inceptionev/PlasmaTransformer/3D Print and CNC/ConformalCoatingJig.stl

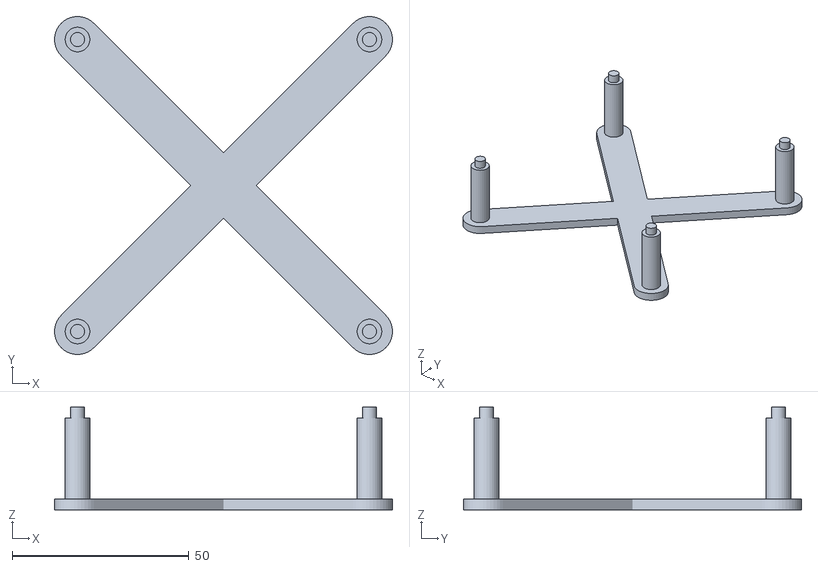
[picture p19: CAD file, 2025-08-11]
3D Print and CNC/ConformalCoatingJig.stl
95.5 x 95.5 x 29.0
