inceptionev/PlasmaTransformer/3D Print and CNC/15cmPasteMaskTemplate.stl

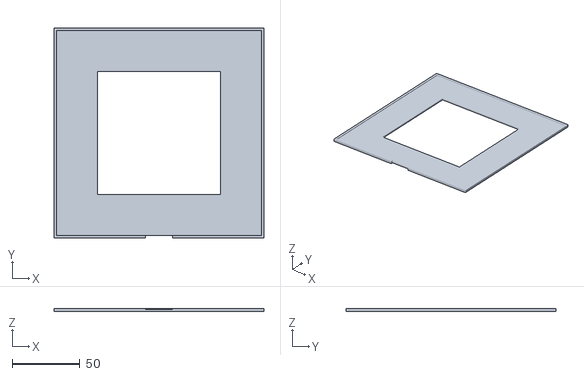
[picture p20: CAD file, 2025-07-31]
3D Print and CNC/15cmPasteMaskTemplate.stl
154.6 x 154.6 x 2.50
