inceptionev/PlasmaTransformer/3D Print and CNC/heatsink-dual-CNC.dxf

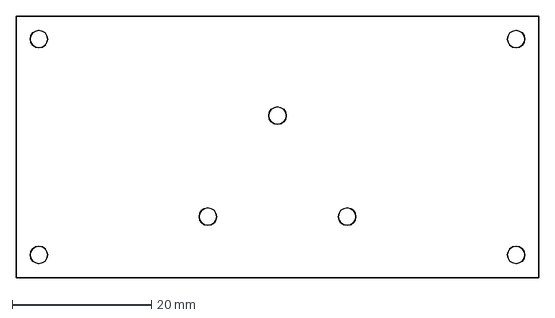
[picture p21: CAD file, 2025-06-07]
3D Print and CNC/heatsink-dual-CNC.dxf
75.0 x 37.5 mm
