inceptionev/PlasmaTransformer/3D Print and CNC/FanShroud-20cm.stl

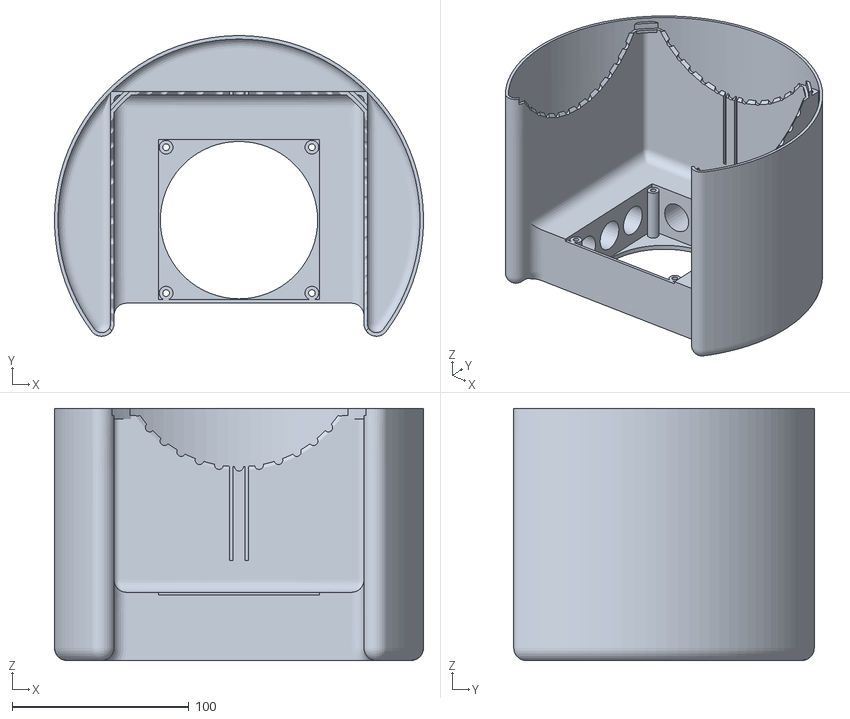
[picture p22: CAD file, 2025-05-27]
3D Print and CNC/FanShroud-20cm.stl
208.8 x 170.1 x 142.6
