inceptionev/PlasmaTransformer/3D Print and CNC/FanShroud-Foot.stl

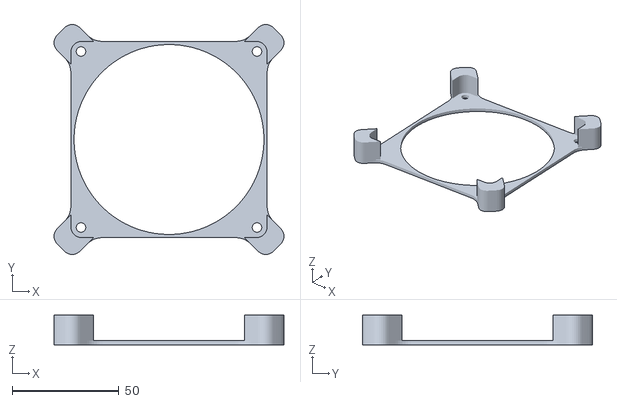
[picture p23: CAD file, 2025-05-27]
3D Print and CNC/FanShroud-Foot.stl
107.8 x 107.8 x 14.0
