inceptionev/PlasmaTransformer/3D Print and CNC/FanShroud.stl

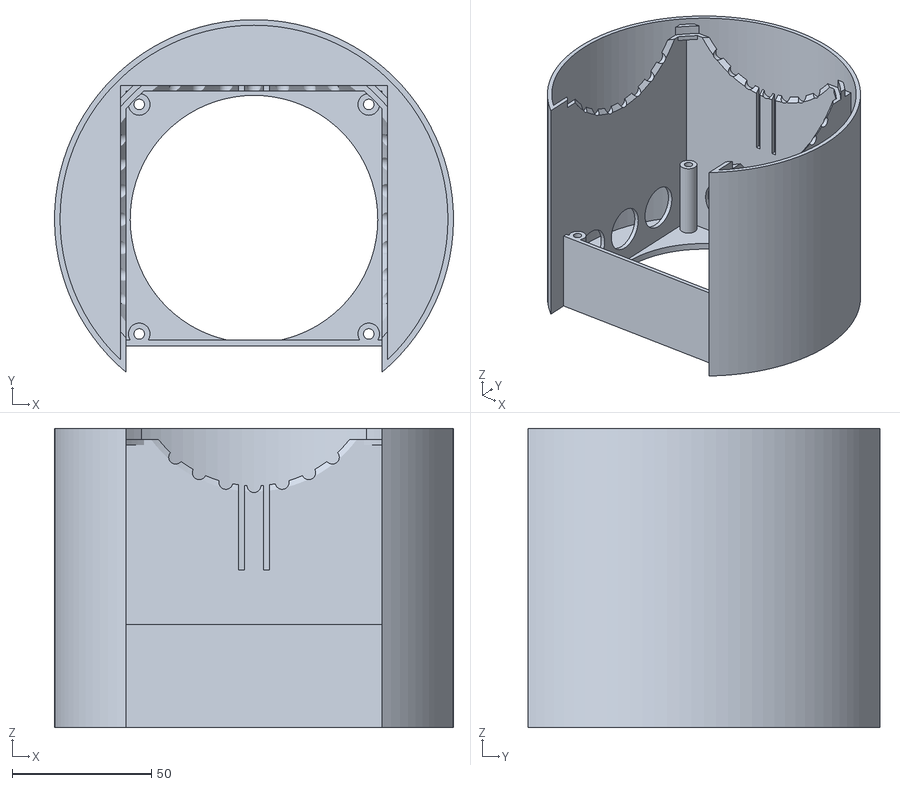
[picture p24: CAD file, 2025-05-20]
3D Print and CNC/FanShroud.stl
143.4 x 126.7 x 107.6
