inceptionev/PlasmaTransformer/3D Print and CNC/heatsink-CNC.stp

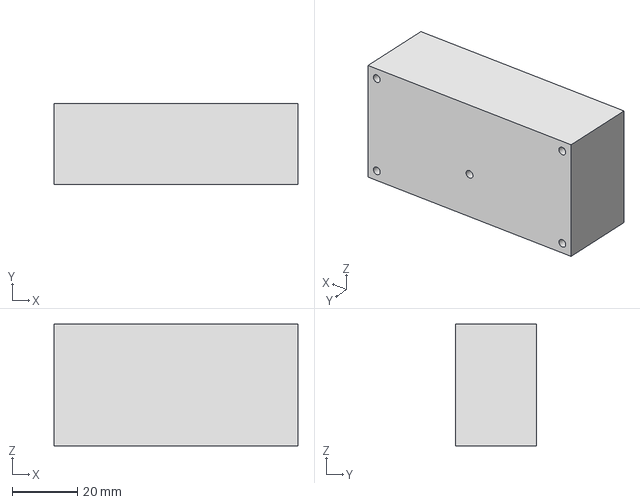
[picture p25: CAD file, 2025-05-20]
3D Print and CNC/heatsink-CNC.stp
75.0 x 25.0 x 37.5 mm
