inceptionev/PlasmaTransformer/LTSPICE/DualFETZVS-LowFreq.asc

C1: cap; 330µF
C2: cap; 6µ
D1: diode; UDZV12B
D2: schottky
D3: zener; UDZV10B
D5: schottky
D6: diode; UDZV12B
Lchoke1: ind; 28µ; Rser=16m
Lchoke3: ind; 28µ; Rser=16m
Lplasma: ind; 0.5µH
Lprimary: ind; 6.2µ; Rser=16m
R1: res; 0
R2: res; 10k
R3: res; 165
R4: res; 1k
R5: res; 1000
R8: res; 1k
R9: res; 0.4k
R10: res; 0.6k
R11: res; 10k
R12: res; 150
R13: res; 47
U1: irfp260n
U2: irfp260n
V1: voltage; 18V
Named nets: 0, GATE1, DRAIN1, GATE2, DRAIN2
POWER SWITCH
FAN
K1 Lprimary Lplasma 0.02
PLASMA RING
POWER INPUT
BIAS CONTROL
SWITCH
FEEDBACK
.tran 0.1 startup
