inceptionev/PlasmaTransformer/LTSPICE/DualFETZVS-Willis.asc

C1: cap; 330µF
C3: cap; 5.6n
C4: cap; 5.6n
C5: cap; 200p
C7: cap; 200p
C8: cap; 200p
C9: cap; 200p
C10: cap; 200p
C11: cap; 200p
D1: diode; UDZV12B
D3: zener; UDZV10B
D6: diode; UDZV12B
Lchoke1: ind; 28µ; Rser=16m
Lchoke3: ind; 28µ; Rser=16m
Lplasma: ind; 0.5µH
Lprimary: ind; 2µ; Rser=16m
R1: res; 0
R2: res; 400
R3: res; 10k
R4: res; 1k
R5: res; 1000
R6: res; 10k
R7: res; 1k
R8: res; 1k
R9: res; 0.4k
R10: res; 0.6k
R11: res; 1k
R13: res; 100
U1: irfp260n
U2: irfp260n
V1: voltage; 18V
Named nets: 0, GATE1, DRAIN1, GATE2, DRAIN2
POWER SWITCH
FAN
K1 Lprimary Lplasma 0.02
PLASMA RING
POWER INPUT
BIAS CONTROL
SWITCH
FEEDBACK
.tran 0.1 startup
