inceptionev/PlasmaTransformer/LTSPICE/DualFETZVS.asc

C1: cap; 330µF
C2: cap; 2.2nF
C3: cap; 10p
C4: cap; 10p
C5: cap; 10p
C6: cap; 10p
C7: cap; 10p
C8: cap; 10p
C9: cap; 2.2nF
D1: diode; UDZV15B
D2: diode; UDZV15B
D3: zener; UDZV10B
Lchoke1: ind; 50µH; Rser=16m
Lchoke2: ind; 50µH; Rser=16m
Lplasma: ind; 0.5µH
Lprimary: ind; 2µH; Rser=16m
R1: res; 0
R2: res; 800
R3: res; 1k
R4: res; 1k
R5: res; 100
R6: res; 10k
R7: res; 10k
R8: res; 1k
R9: res; 0.2k
R10: res; 0.8k
U1: irfp260n
U2: irfp260n
V1: voltage; 18V
Named nets: 0, GATE1, DRAIN1, GATE2, DRAIN2
POWER SWITCH
FAN
K1 Lprimary Lplasma 0.2
PLASMA RING
POWER INPUT
BIAS CONTROL
SWITCH
FEEDBACK
.tran 0.1 startup
