inceptionev/PlasmaTransformer/LTSPICE/NikolaToy-PlasmaToroidDriver.asc

C1: cap; 330µF
C2: cap; 220pF
C3: cap; 220p
C4: cap; 220pF
C6: cap; 4.9nF
C7: cap; 4.9nF
D1: TVSdiode; TDZV15
D3: diode; UDZV10B
Lchoke: ind; 11µH; Rser=16m
Lplasma: ind; 0.5µH
Lprimary: ind; 2µH; Rser=16m
R1: res; 0
R2: res; 1k
R3: res; 0.9k
R4: res; 0.1k
R5: res; 100
R8: res; 1k
R9: res; 1k
R10: res; 1.8k
R11: res; 3k
Rgate: res; 0
U1: irfp260n
V1: voltage; 15V
Named nets: 0, GATE, DRAIN
POWER SWITCH
POTENTIOMETER
LOW
HIGH
FAN
K1 Lprimary Lplasma 0.2
PLASMA RING
POWER INPUT
BIAS CONTROL
SWITCH
FEEDBACK
.tran 1 startup
